SpikeWils/OpenCut/OpenCut Src & Docs/OpenCut Src/OpenCut Machine Software/CableIDPrinter.cpp

// CableIDPrinter.cpp

#include "CableIDPrinter.h"

const int minChar = 32;
const int maxChar = 96;
const int rowsPerChar = 10;
const int fontSize = (maxChar - minChar + 1) * rowsPerChar;
const word font[fontSize] = {

  // ASCII 032-048; $20-$2F
  // 'Space' thru "/"
  0b0000000000000000,
  0b0000000000000000,
  0b0000000000000000,
  0b0000000000000000,
  0b0000000000000000,
  0b0000000000000000,
  0b0000000000000000,
  0b0000000000000000,
  0b0000000000000000,
  0b0000000000000000,
  // '!'
  0b0000000000000000,
  0b0000000000000000,
  0b0000000000000000,
  0b0000000000000000,
  0b0000111111110011,
  0b0000111111110011,
  0b0000000000000000,
  0b0000000000000000,
  0b0000000000000000,
  0b0000000000000000,
  // '"'
  0b0000000000000000,
  0b0000000000000000,
  0b0000111000000000,
  0b0000111000000000,
  0b0000000000000000,
  0b0000000000000000,
  0b0000111000000000,
  0b0000111000000000,
  0b0000000000000000,
  0b0000000000000000,
  // '#'
  0b0000000110011000,
  0b0000000110011110,
  0b0000000111111110,
  0b0000011111111000,
  0b0000011110011000,
  0b0000000110011110,
  0b0000000111111110,
  0b0000011111111000,
  0b0000011110011000,
  0b0000000110011000,
  // '$'
  0b0000001100001100,
  0b0000011110001110,
  0b0000010011000010,
  0b0000010011000010,
  0b0000111111111111,
  0b0000111111111111,
  0b0000010000110010,
  0b0000010000110010,
  0b0000011100011110,
  0b0000001100001100,
  // '%'
  0b0000001100000110,
  0b000001001001110,
  0b0000010010011100,
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
    spray_letter(asciiValue);
  }
}

void CableIDPrinter::spray_letter(int letter) {
  if (letter >= minChar && letter <= maxChar) {
    for (int row = 0; row < rowsPerChar; row++) {
      word strip = font[((letter - minChar) * rowsPerChar) + row];
      _inkShield.spray_ink(strip);
    }
  }
}
